AayanShaikh007/scalars-keyboard/PCB/keyboard.kicad_sch

## KiCad design PCB/keyboard.kicad_sch (2025-06-13)

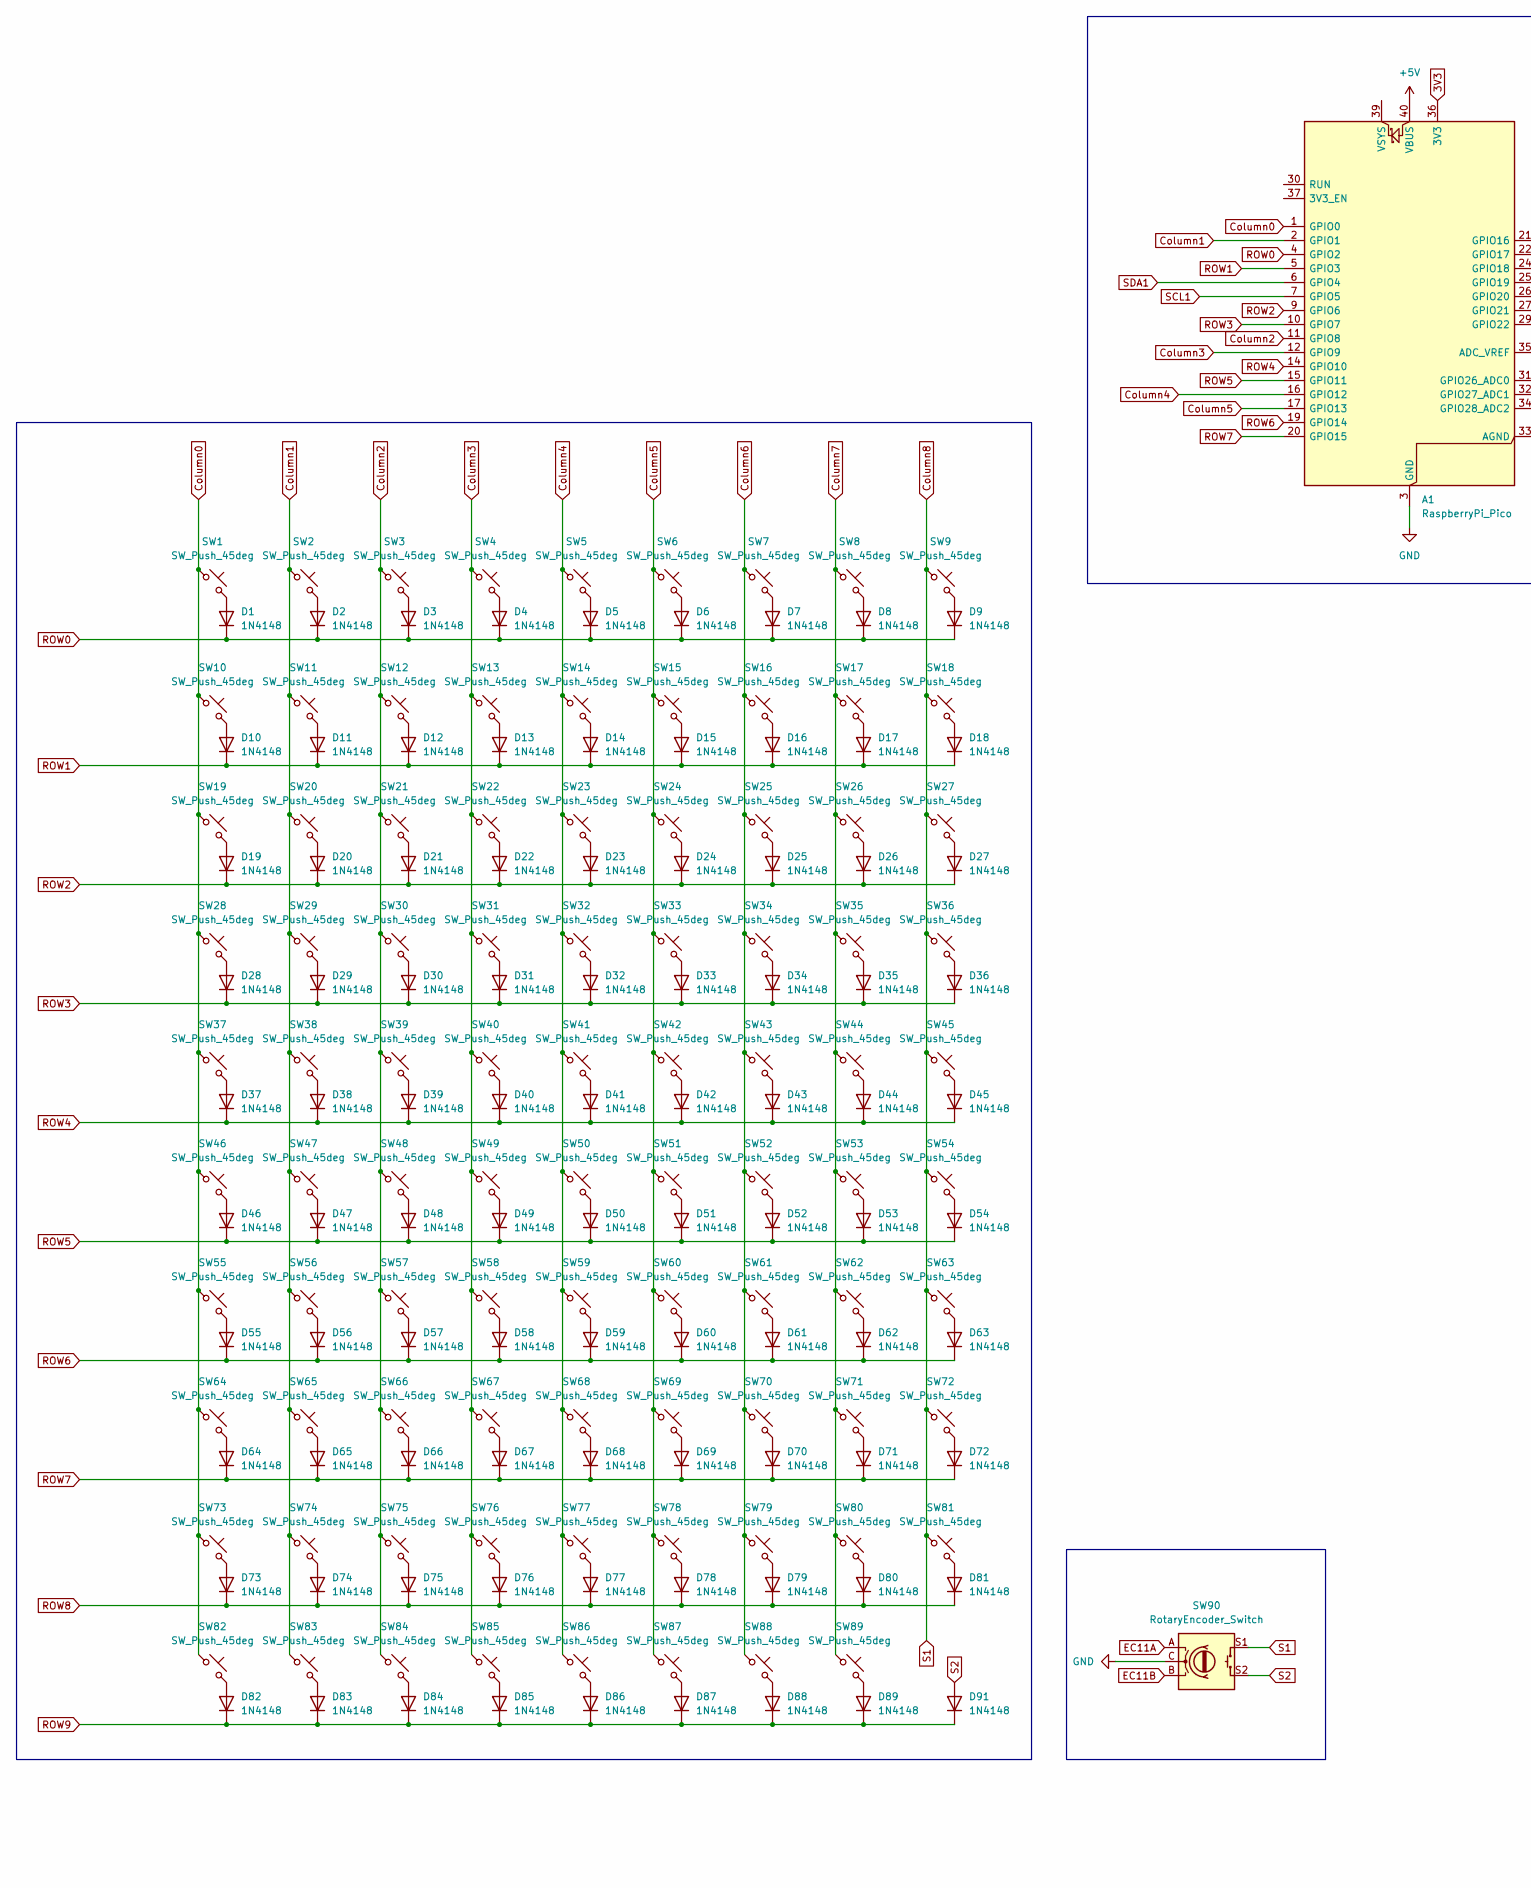
[picture p3: schematic keyboard.kicad_sch, part in row 1, column 1]

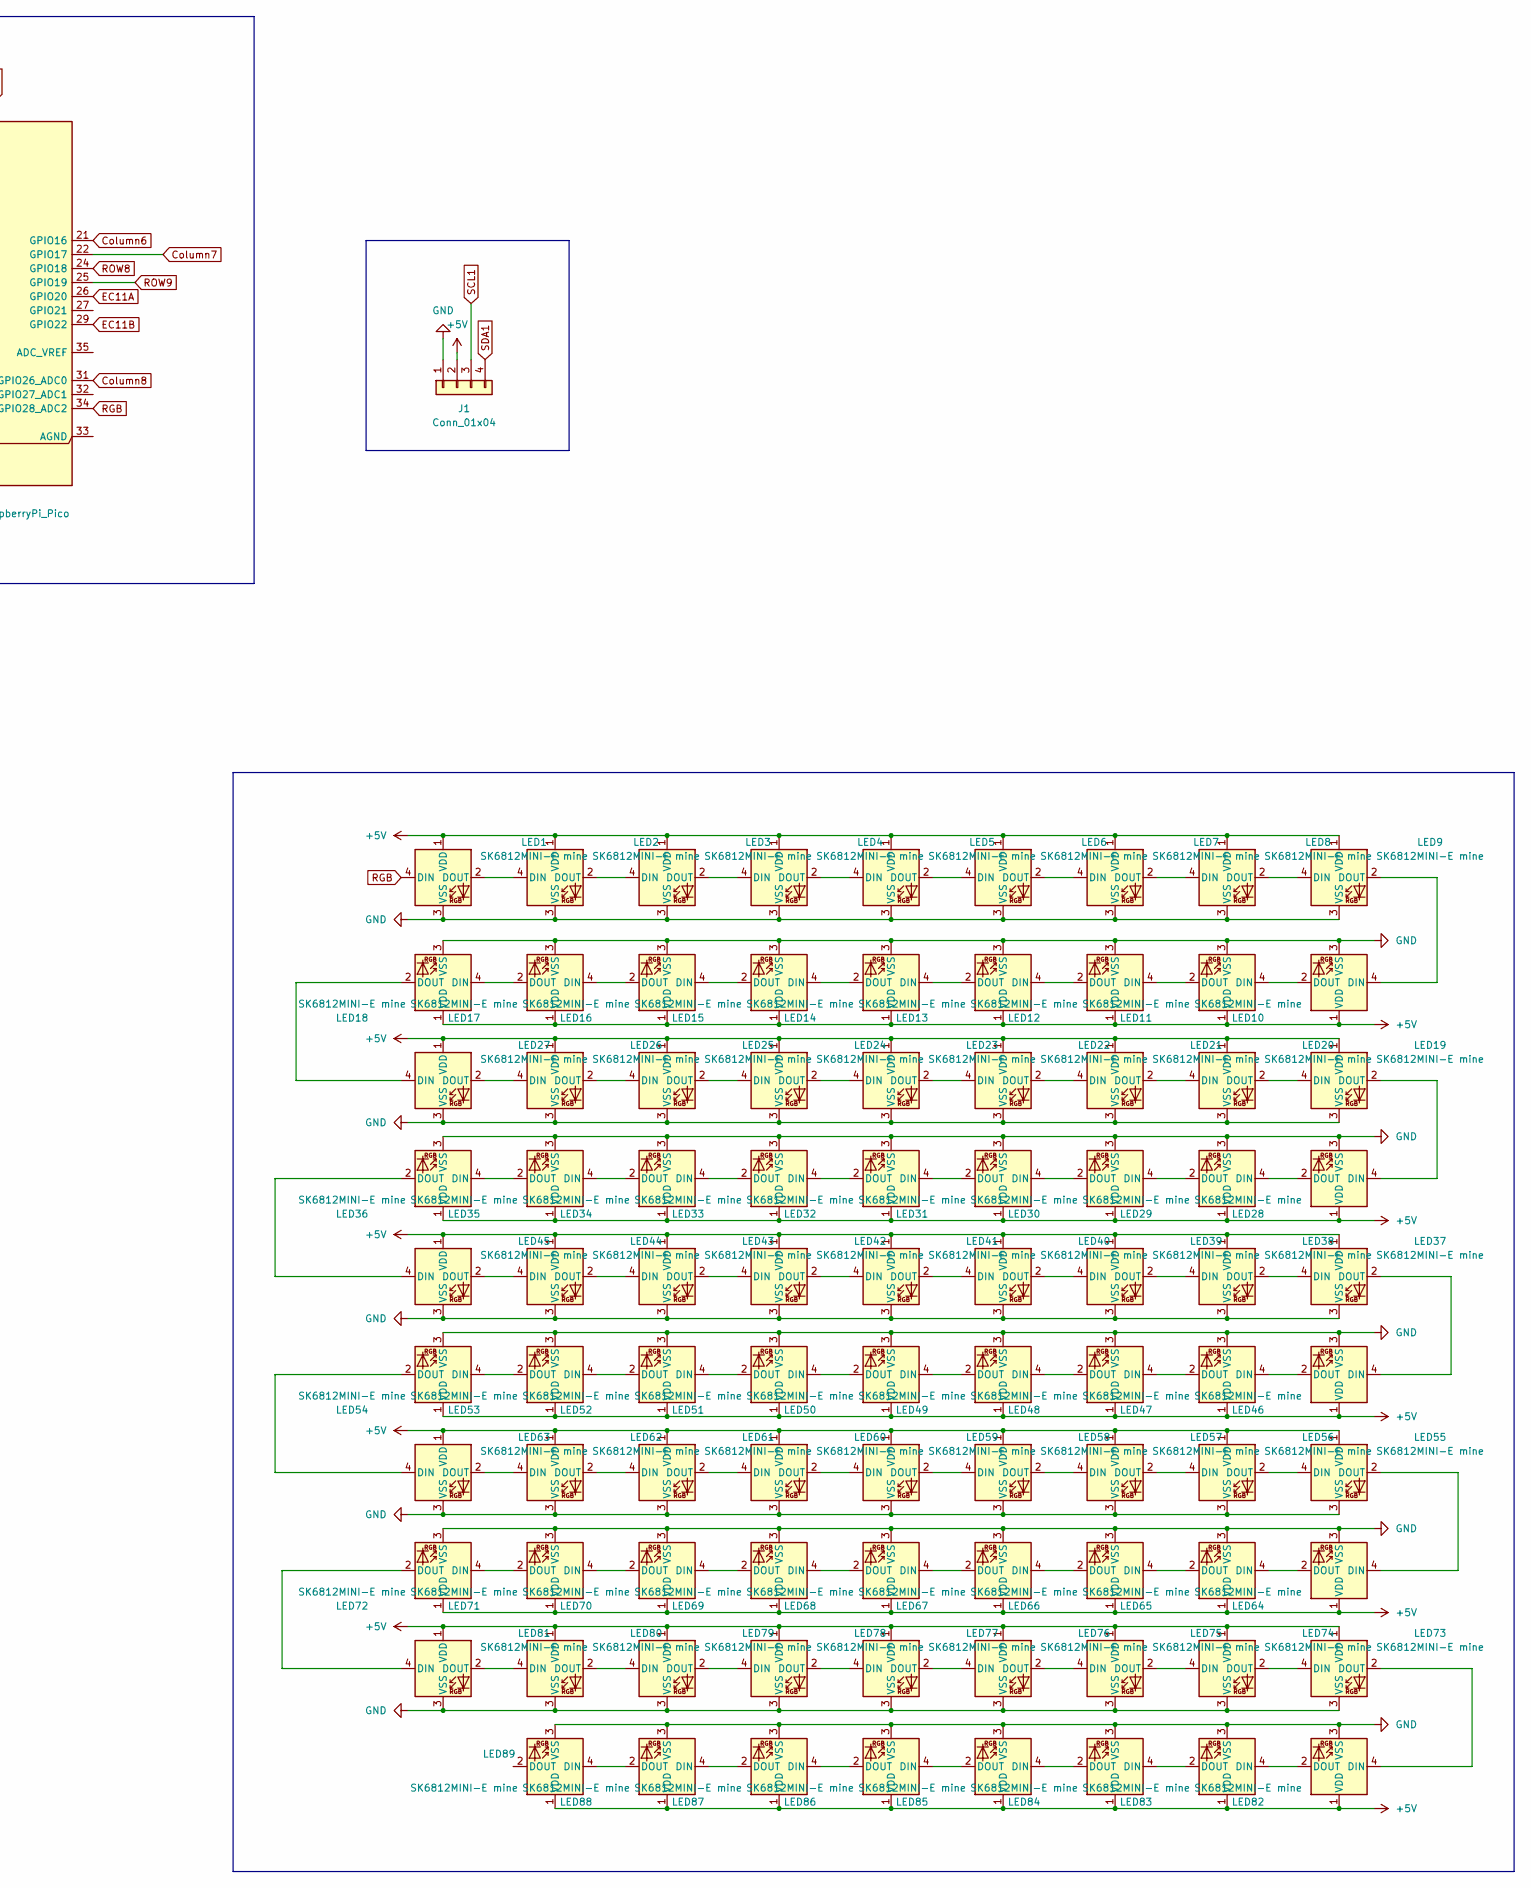
[picture p4: schematic keyboard.kicad_sch, part in row 1, column 2]

Parts:
A1: RaspberryPi_Pico; RaspberryPi_Pico_Common_THT
D1, D2, D3, D4, D5, D6, D7, D8, D9, D10, D11, D12, D13, D14, D15, D16, D17, D18, D19, D20, D21, D22, D23, D24, D25, D26, D27, D28, D29, D30, D31, D32, D33, D34, D35, D36, D37, D38, D39, D40, D41, D42, D43, D44, D45, D46, D47, D48, D49, D50, D51, D52, D53, D54, D55, D56, D57, D58, D59, D60, D61, D62, D63, D64, D65, D66, D67, D68, D69, D70, D71, D72, D73, D74, D75, D76, D77, D78, D79, D80, D81, D82, D83, D84, D85, D86, D87, D88, D89, D91: 1N4148; DO35-7
J1: Conn_01x04; SSD1306-0.91-OLED-4pin-128x32
LED1, LED2, LED3, LED4, LED5, LED6, LED7, LED8, LED9, LED10, LED11, LED12, LED13, LED14, LED15, LED16, LED17, LED18, LED19, LED20, LED21, LED22, LED23, LED24, LED25, LED26, LED27, LED28, LED29, LED30, LED31, LED32, LED33, LED34, LED35, LED36, LED37, LED38, LED39, LED40, LED41, LED42, LED43, LED44, LED45, LED46, LED47, LED48, LED49, LED50, LED51, LED52, LED53, LED54, LED55, LED56, LED57, LED58, LED59, LED60, LED61, LED62, LED63, LED64, LED65, LED66, LED67, LED68, LED69, LED70, LED71, LED72, LED73, LED74, LED75, LED76, LED77, LED78, LED79, LED80, LED81, LED82, LED83, LED84, LED85, LED86, LED87, LED88, LED89: SK6812MINI-E mine; BAcklight
SW1, SW2, SW3, SW4, SW5, SW6, SW7, SW8, SW9, SW10, SW11, SW12, SW13, SW14, SW15, SW16, SW17, SW18, SW19, SW20, SW21, SW22, SW23, SW24, SW25, SW26, SW27, SW28, SW29, SW30, SW31, SW32, SW33, SW34, SW35, SW36, SW37, SW38, SW39, SW40, SW41, SW42, SW43, SW44, SW45, SW46, SW47, SW48, SW49, SW50, SW51, SW52, SW53, SW54, SW55, SW56, SW57, SW58, SW59, SW60, SW61, SW62, SW63, SW64, SW65, SW66, SW67, SW68, SW69, SW70, SW71, SW72, SW73, SW74, SW75: SW_Push_45deg; SW_Hotswap_Kailh_MX_1.00u
SW76, SW77, SW78, SW79, SW80: SW_Push_45deg; SW_Hotswap_Kailh_MX_1.25u
SW81, SW82, SW83: SW_Push_45deg; SW_Hotswap_Kailh_MX_1.50u
SW84: SW_Push_45deg; SW_Hotswap_Kailh_MX_1.75u
SW85: SW_Push_45deg; SW_Hotswap_Kailh_MX_2.00u
SW86, SW87: SW_Push_45deg; SW_Hotswap_Kailh_MX_2.25u
SW88: SW_Push_45deg; SW_Hotswap_Kailh_MX_2.75u
SW89: SW_Push_45deg; SW_Hotswap_Kailh_MX_6.25u
SW90: RotaryEncoder_Switch; RotaryEncoder_Alps_EC11E-Switch_Vertical_H20mm

Connections:
3V3: A1.36 (3V3)
+5V: A1.40 (VBUS), J1.2, LED1.1 (VDD), LED2.1 (VDD), LED3.1 (VDD), LED4.1 (VDD), LED5.1 (VDD), LED6.1 (VDD), LED7.1 (VDD), LED8.1 (VDD), LED9.1 (VDD), LED10.1 (VDD), LED11.1 (VDD), LED12.1 (VDD), LED13.1 (VDD), LED14.1 (VDD), LED15.1 (VDD), LED16.1 (VDD), LED17.1 (VDD), LED18.1 (VDD), LED19.1 (VDD), LED20.1 (VDD), LED21.1 (VDD), LED22.1 (VDD), LED23.1 (VDD), LED24.1 (VDD), LED25.1 (VDD), LED26.1 (VDD), LED27.1 (VDD), LED28.1 (VDD), LED29.1 (VDD), LED30.1 (VDD), LED31.1 (VDD), LED32.1 (VDD), LED33.1 (VDD), LED34.1 (VDD), LED35.1 (VDD), LED36.1 (VDD), LED37.1 (VDD), LED38.1 (VDD), LED39.1 (VDD), LED40.1 (VDD), LED41.1 (VDD), LED42.1 (VDD), LED43.1 (VDD), LED44.1 (VDD), LED45.1 (VDD), LED46.1 (VDD), LED47.1 (VDD), LED48.1 (VDD), LED49.1 (VDD), LED50.1 (VDD), LED51.1 (VDD), LED52.1 (VDD), LED53.1 (VDD), LED54.1 (VDD), LED55.1 (VDD), LED56.1 (VDD), LED57.1 (VDD), LED58.1 (VDD), LED59.1 (VDD), LED60.1 (VDD), LED61.1 (VDD), LED62.1 (VDD), LED63.1 (VDD), LED64.1 (VDD), LED65.1 (VDD), LED66.1 (VDD), LED67.1 (VDD), LED68.1 (VDD), LED69.1 (VDD), LED70.1 (VDD), LED71.1 (VDD), LED72.1 (VDD), LED73.1 (VDD), LED74.1 (VDD), LED75.1 (VDD), LED76.1 (VDD), LED77.1 (VDD), LED78.1 (VDD), LED79.1 (VDD), LED80.1 (VDD), LED81.1 (VDD), LED82.1 (VDD), LED83.1 (VDD), LED84.1 (VDD), LED85.1 (VDD), LED86.1 (VDD), LED87.1 (VDD), LED88.1 (VDD), LED89.1 (VDD)
Column0: A1.1 (GPIO0), SW1.1, SW10.1, SW19.1, SW28.1, SW37.1, SW46.1, SW55.1, SW64.1, SW73.1, SW82.1
Column1: A1.2 (GPIO1), SW2.1, SW11.1, SW20.1, SW29.1, SW38.1, SW47.1, SW56.1, SW65.1, SW74.1, SW83.1
Column2: A1.11 (GPIO8), SW3.1, SW12.1, SW21.1, SW30.1, SW39.1, SW48.1, SW57.1, SW66.1, SW75.1, SW84.1
Column3: A1.12 (GPIO9), SW4.1, SW13.1, SW22.1, SW31.1, SW40.1, SW49.1, SW58.1, SW67.1, SW76.1, SW85.1
Column4: A1.16 (GPIO12), SW5.1, SW14.1, SW23.1, SW32.1, SW41.1, SW50.1, SW59.1, SW68.1, SW77.1, SW86.1
Column5: A1.17 (GPIO13), SW6.1, SW15.1, SW24.1, SW33.1, SW42.1, SW51.1, SW60.1, SW69.1, SW78.1, SW87.1
Column6: A1.21 (GPIO16), SW7.1, SW16.1, SW25.1, SW34.1, SW43.1, SW52.1, SW61.1, SW70.1, SW79.1, SW88.1
Column7: A1.22 (GPIO17), SW8.1, SW17.1, SW26.1, SW35.1, SW44.1, SW53.1, SW62.1, SW71.1, SW80.1, SW89.1
Column8: A1.31 (GPIO26_ADC0), SW9.1, SW18.1, SW27.1, SW36.1, SW45.1, SW54.1, SW63.1, SW72.1, SW81.1, SW90.S1
EC11A: A1.26 (GPIO20), SW90.A
EC11B: A1.29 (GPIO22), SW90.B
GND: A1.3 (GND), A1.8 (GND), A1.13 (GND), A1.18 (GND), A1.23 (GND), A1.28 (GND), A1.38 (GND), J1.1, LED1.3 (VSS), LED2.3 (VSS), LED3.3 (VSS), LED4.3 (VSS), LED5.3 (VSS), LED6.3 (VSS), LED7.3 (VSS), LED8.3 (VSS), LED9.3 (VSS), LED10.3 (VSS), LED11.3 (VSS), LED12.3 (VSS), LED13.3 (VSS), LED14.3 (VSS), LED15.3 (VSS), LED16.3 (VSS), LED17.3 (VSS), LED18.3 (VSS), LED19.3 (VSS), LED20.3 (VSS), LED21.3 (VSS), LED22.3 (VSS), LED23.3 (VSS), LED24.3 (VSS), LED25.3 (VSS), LED26.3 (VSS), LED27.3 (VSS), LED28.3 (VSS), LED29.3 (VSS), LED30.3 (VSS), LED31.3 (VSS), LED32.3 (VSS), LED33.3 (VSS), LED34.3 (VSS), LED35.3 (VSS), LED36.3 (VSS), LED37.3 (VSS), LED38.3 (VSS), LED39.3 (VSS), LED40.3 (VSS), LED41.3 (VSS), LED42.3 (VSS), LED43.3 (VSS), LED44.3 (VSS), LED45.3 (VSS), LED46.3 (VSS), LED47.3 (VSS), LED48.3 (VSS), LED49.3 (VSS), LED50.3 (VSS), LED51.3 (VSS), LED52.3 (VSS), LED53.3 (VSS), LED54.3 (VSS), LED55.3 (VSS), LED56.3 (VSS), LED57.3 (VSS), LED58.3 (VSS), LED59.3 (VSS), LED60.3 (VSS), LED61.3 (VSS), LED62.3 (VSS), LED63.3 (VSS), LED64.3 (VSS), LED65.3 (VSS), LED66.3 (VSS), LED67.3 (VSS), LED68.3 (VSS), LED69.3 (VSS), LED70.3 (VSS), LED71.3 (VSS), LED72.3 (VSS), LED73.3 (VSS), LED74.3 (VSS), LED75.3 (VSS), LED76.3 (VSS), LED77.3 (VSS), LED78.3 (VSS), LED79.3 (VSS), LED80.3 (VSS), LED81.3 (VSS), LED82.3 (VSS), LED83.3 (VSS), LED84.3 (VSS), LED85.3 (VSS), LED86.3 (VSS), LED87.3 (VSS), LED88.3 (VSS), LED89.3 (VSS), SW90.C
unnamed: D1.2 (A), SW1.2
unnamed: D2.2 (A), SW2.2
unnamed: D3.2 (A), SW3.2
unnamed: D4.2 (A), SW4.2
unnamed: D5.2 (A), SW5.2
unnamed: D6.2 (A), SW6.2
unnamed: D7.2 (A), SW7.2
unnamed: D8.2 (A), SW8.2
unnamed: D9.2 (A), SW9.2
unnamed: D10.2 (A), SW10.2
unnamed: D11.2 (A), SW11.2
unnamed: D12.2 (A), SW12.2
unnamed: D13.2 (A), SW13.2
unnamed: D14.2 (A), SW14.2
unnamed: D15.2 (A), SW15.2
unnamed: D16.2 (A), SW16.2
unnamed: D17.2 (A), SW17.2
unnamed: D18.2 (A), SW18.2
unnamed: D19.2 (A), SW19.2
unnamed: D20.2 (A), SW20.2
unnamed: D21.2 (A), SW21.2
unnamed: D22.2 (A), SW22.2
unnamed: D23.2 (A), SW23.2
unnamed: D24.2 (A), SW24.2
unnamed: D25.2 (A), SW25.2
unnamed: D26.2 (A), SW26.2
unnamed: D27.2 (A), SW27.2
unnamed: D28.2 (A), SW28.2
unnamed: D29.2 (A), SW29.2
unnamed: D30.2 (A), SW30.2
unnamed: D31.2 (A), SW31.2
unnamed: D32.2 (A), SW32.2
unnamed: D33.2 (A), SW33.2
unnamed: D34.2 (A), SW34.2
unnamed: D35.2 (A), SW35.2
unnamed: D36.2 (A), SW36.2
unnamed: D37.2 (A), SW37.2
unnamed: D38.2 (A), SW38.2
unnamed: D39.2 (A), SW39.2
unnamed: D40.2 (A), SW40.2
unnamed: D41.2 (A), SW41.2
unnamed: D42.2 (A), SW42.2
unnamed: D43.2 (A), SW43.2
unnamed: D44.2 (A), SW44.2
unnamed: D45.2 (A), SW45.2
unnamed: D46.2 (A), SW46.2
unnamed: D47.2 (A), SW47.2
unnamed: D48.2 (A), SW48.2
unnamed: D49.2 (A), SW49.2
unnamed: D50.2 (A), SW50.2
unnamed: D51.2 (A), SW51.2
unnamed: D52.2 (A), SW52.2
unnamed: D53.2 (A), SW53.2
unnamed: D54.2 (A), SW54.2
unnamed: D55.2 (A), SW55.2
unnamed: D56.2 (A), SW56.2
unnamed: D57.2 (A), SW57.2
unnamed: D58.2 (A), SW58.2
unnamed: D59.2 (A), SW59.2
unnamed: D60.2 (A), SW60.2
unnamed: D61.2 (A), SW61.2
unnamed: D62.2 (A), SW62.2
unnamed: D63.2 (A), SW63.2
unnamed: D64.2 (A), SW64.2
unnamed: D65.2 (A), SW65.2
unnamed: D66.2 (A), SW66.2
unnamed: D67.2 (A), SW67.2
unnamed: D68.2 (A), SW68.2
unnamed: D69.2 (A), SW69.2
unnamed: D70.2 (A), SW70.2
unnamed: D71.2 (A), SW71.2
unnamed: D72.2 (A), SW72.2
unnamed: D73.2 (A), SW73.2
unnamed: D74.2 (A), SW74.2
unnamed: D75.2 (A), SW75.2
unnamed: D76.2 (A), SW76.2
unnamed: D77.2 (A), SW77.2
unnamed: D78.2 (A), SW78.2
unnamed: D79.2 (A), SW79.2
unnamed: D80.2 (A), SW80.2
unnamed: D81.2 (A), SW81.2
unnamed: D82.2 (A), SW82.2
unnamed: D83.2 (A), SW83.2
unnamed: D84.2 (A), SW84.2
unnamed: D85.2 (A), SW85.2
unnamed: D86.2 (A), SW86.2
unnamed: D87.2 (A), SW87.2
unnamed: D88.2 (A), SW88.2
unnamed: D89.2 (A), SW89.2
unnamed: LED1.2 (DOUT), LED2.4 (DIN)
unnamed: LED2.2 (DOUT), LED3.4 (DIN)
unnamed: LED3.2 (DOUT), LED4.4 (DIN)
unnamed: LED4.2 (DOUT), LED5.4 (DIN)
unnamed: LED5.2 (DOUT), LED6.4 (DIN)
unnamed: LED6.2 (DOUT), LED7.4 (DIN)
unnamed: LED7.2 (DOUT), LED8.4 (DIN)
unnamed: LED8.2 (DOUT), LED9.4 (DIN)
unnamed: LED10.2 (DOUT), LED11.4 (DIN)
unnamed: LED9.2 (DOUT), LED10.4 (DIN)
unnamed: LED11.2 (DOUT), LED12.4 (DIN)
unnamed: LED12.2 (DOUT), LED13.4 (DIN)
unnamed: LED13.2 (DOUT), LED14.4 (DIN)
unnamed: LED14.2 (DOUT), LED15.4 (DIN)
unnamed: LED15.2 (DOUT), LED16.4 (DIN)
unnamed: LED16.2 (DOUT), LED17.4 (DIN)
unnamed: LED17.2 (DOUT), LED18.4 (DIN)
unnamed: LED18.2 (DOUT), LED27.4 (DIN)
unnamed: LED19.2 (DOUT), LED28.4 (DIN)
unnamed: LED19.4 (DIN), LED20.2 (DOUT)
unnamed: LED20.4 (DIN), LED21.2 (DOUT)
unnamed: LED21.4 (DIN), LED22.2 (DOUT)
unnamed: LED22.4 (DIN), LED23.2 (DOUT)
unnamed: LED23.4 (DIN), LED24.2 (DOUT)
unnamed: LED24.4 (DIN), LED25.2 (DOUT)
unnamed: LED25.4 (DIN), LED26.2 (DOUT)
unnamed: LED26.4 (DIN), LED27.2 (DOUT)
unnamed: LED28.2 (DOUT), LED29.4 (DIN)
unnamed: LED29.2 (DOUT), LED30.4 (DIN)
unnamed: LED30.2 (DOUT), LED31.4 (DIN)
unnamed: LED31.2 (DOUT), LED32.4 (DIN)
unnamed: LED32.2 (DOUT), LED33.4 (DIN)
unnamed: LED33.2 (DOUT), LED34.4 (DIN)
unnamed: LED34.2 (DOUT), LED35.4 (DIN)
unnamed: LED35.2 (DOUT), LED36.4 (DIN)
unnamed: LED36.2 (DOUT), LED45.4 (DIN)
unnamed: LED37.2 (DOUT), LED46.4 (DIN)
unnamed: LED37.4 (DIN), LED38.2 (DOUT)
unnamed: LED38.4 (DIN), LED39.2 (DOUT)
unnamed: LED39.4 (DIN), LED40.2 (DOUT)
unnamed: LED40.4 (DIN), LED41.2 (DOUT)
unnamed: LED41.4 (DIN), LED42.2 (DOUT)
unnamed: LED42.4 (DIN), LED43.2 (DOUT)
unnamed: LED43.4 (DIN), LED44.2 (DOUT)
unnamed: LED44.4 (DIN), LED45.2 (DOUT)
unnamed: LED46.2 (DOUT), LED47.4 (DIN)
unnamed: LED47.2 (DOUT), LED48.4 (DIN)
unnamed: LED48.2 (DOUT), LED49.4 (DIN)
unnamed: LED49.2 (DOUT), LED50.4 (DIN)
unnamed: LED50.2 (DOUT), LED51.4 (DIN)
unnamed: LED51.2 (DOUT), LED52.4 (DIN)
unnamed: LED52.2 (DOUT), LED53.4 (DIN)
unnamed: LED53.2 (DOUT), LED54.4 (DIN)
unnamed: LED54.2 (DOUT), LED63.4 (DIN)
unnamed: LED55.2 (DOUT), LED64.4 (DIN)
unnamed: LED55.4 (DIN), LED56.2 (DOUT)
unnamed: LED56.4 (DIN), LED57.2 (DOUT)
unnamed: LED57.4 (DIN), LED58.2 (DOUT)
unnamed: LED58.4 (DIN), LED59.2 (DOUT)
unnamed: LED59.4 (DIN), LED60.2 (DOUT)
unnamed: LED60.4 (DIN), LED61.2 (DOUT)
unnamed: LED61.4 (DIN), LED62.2 (DOUT)
unnamed: LED62.4 (DIN), LED63.2 (DOUT)
unnamed: LED64.2 (DOUT), LED65.4 (DIN)
unnamed: LED65.2 (DOUT), LED66.4 (DIN)
unnamed: LED66.2 (DOUT), LED67.4 (DIN)
unnamed: LED67.2 (DOUT), LED68.4 (DIN)
unnamed: LED68.2 (DOUT), LED69.4 (DIN)
unnamed: LED69.2 (DOUT), LED70.4 (DIN)
unnamed: LED70.2 (DOUT), LED71.4 (DIN)
unnamed: LED71.2 (DOUT), LED72.4 (DIN)
unnamed: LED72.2 (DOUT), LED81.4 (DIN)
unnamed: LED73.2 (DOUT), LED82.4 (DIN)
unnamed: LED73.4 (DIN), LED74.2 (DOUT)
unnamed: LED74.4 (DIN), LED75.2 (DOUT)
unnamed: LED75.4 (DIN), LED76.2 (DOUT)
unnamed: LED76.4 (DIN), LED77.2 (DOUT)
unnamed: LED77.4 (DIN), LED78.2 (DOUT)
unnamed: LED78.4 (DIN), LED79.2 (DOUT)
unnamed: LED79.4 (DIN), LED80.2 (DOUT)
unnamed: LED80.4 (DIN), LED81.2 (DOUT)
unnamed: LED82.2 (DOUT), LED83.4 (DIN)
unnamed: LED83.2 (DOUT), LED84.4 (DIN)
unnamed: LED84.2 (DOUT), LED85.4 (DIN)
unnamed: LED85.2 (DOUT), LED86.4 (DIN)
unnamed: LED86.2 (DOUT), LED87.4 (DIN)
unnamed: LED87.2 (DOUT), LED88.4 (DIN)
unnamed: LED88.2 (DOUT), LED89.4 (DIN)
RGB: A1.34 (GPIO28_ADC2), LED1.4 (DIN)
ROW0: A1.4 (GPIO2), D1.1 (K), D2.1 (K), D3.1 (K), D4.1 (K), D5.1 (K), D6.1 (K), D7.1 (K), D8.1 (K), D9.1 (K)
ROW1: A1.5 (GPIO3), D10.1 (K), D11.1 (K), D12.1 (K), D13.1 (K), D14.1 (K), D15.1 (K), D16.1 (K), D17.1 (K), D18.1 (K)
ROW2: A1.9 (GPIO6), D19.1 (K), D20.1 (K), D21.1 (K), D22.1 (K), D23.1 (K), D24.1 (K), D25.1 (K), D26.1 (K), D27.1 (K)
ROW3: A1.10 (GPIO7), D28.1 (K), D29.1 (K), D30.1 (K), D31.1 (K), D32.1 (K), D33.1 (K), D34.1 (K), D35.1 (K), D36.1 (K)
ROW4: A1.14 (GPIO10), D37.1 (K), D38.1 (K), D39.1 (K), D40.1 (K), D41.1 (K), D42.1 (K), D43.1 (K), D44.1 (K), D45.1 (K)
ROW5: A1.15 (GPIO11), D46.1 (K), D47.1 (K), D48.1 (K), D49.1 (K), D50.1 (K), D51.1 (K), D52.1 (K), D53.1 (K), D54.1 (K)
ROW6: A1.19 (GPIO14), D55.1 (K), D56.1 (K), D57.1 (K), D58.1 (K), D59.1 (K), D60.1 (K), D61.1 (K), D62.1 (K), D63.1 (K)
ROW7: A1.20 (GPIO15), D64.1 (K), D65.1 (K), D66.1 (K), D67.1 (K), D68.1 (K), D69.1 (K), D70.1 (K), D71.1 (K), D72.1 (K)
ROW8: A1.24 (GPIO18), D73.1 (K), D74.1 (K), D75.1 (K), D76.1 (K), D77.1 (K), D78.1 (K), D79.1 (K), D80.1 (K), D81.1 (K)
ROW9: A1.25 (GPIO19), D82.1 (K), D83.1 (K), D84.1 (K), D85.1 (K), D86.1 (K), D87.1 (K), D88.1 (K), D89.1 (K), D91.1 (K)
S2: D91.2 (A), SW90.S2
SCL1: A1.7 (GPIO5), J1.3
SDA1: A1.6 (GPIO4), J1.4
